iolo/a2ext/hw/a2ext-carrier/a2ext-carrier.kicad_sch

## KiCad design hw/a2ext-carrier/a2ext-carrier.kicad_sch (2026-09-17)

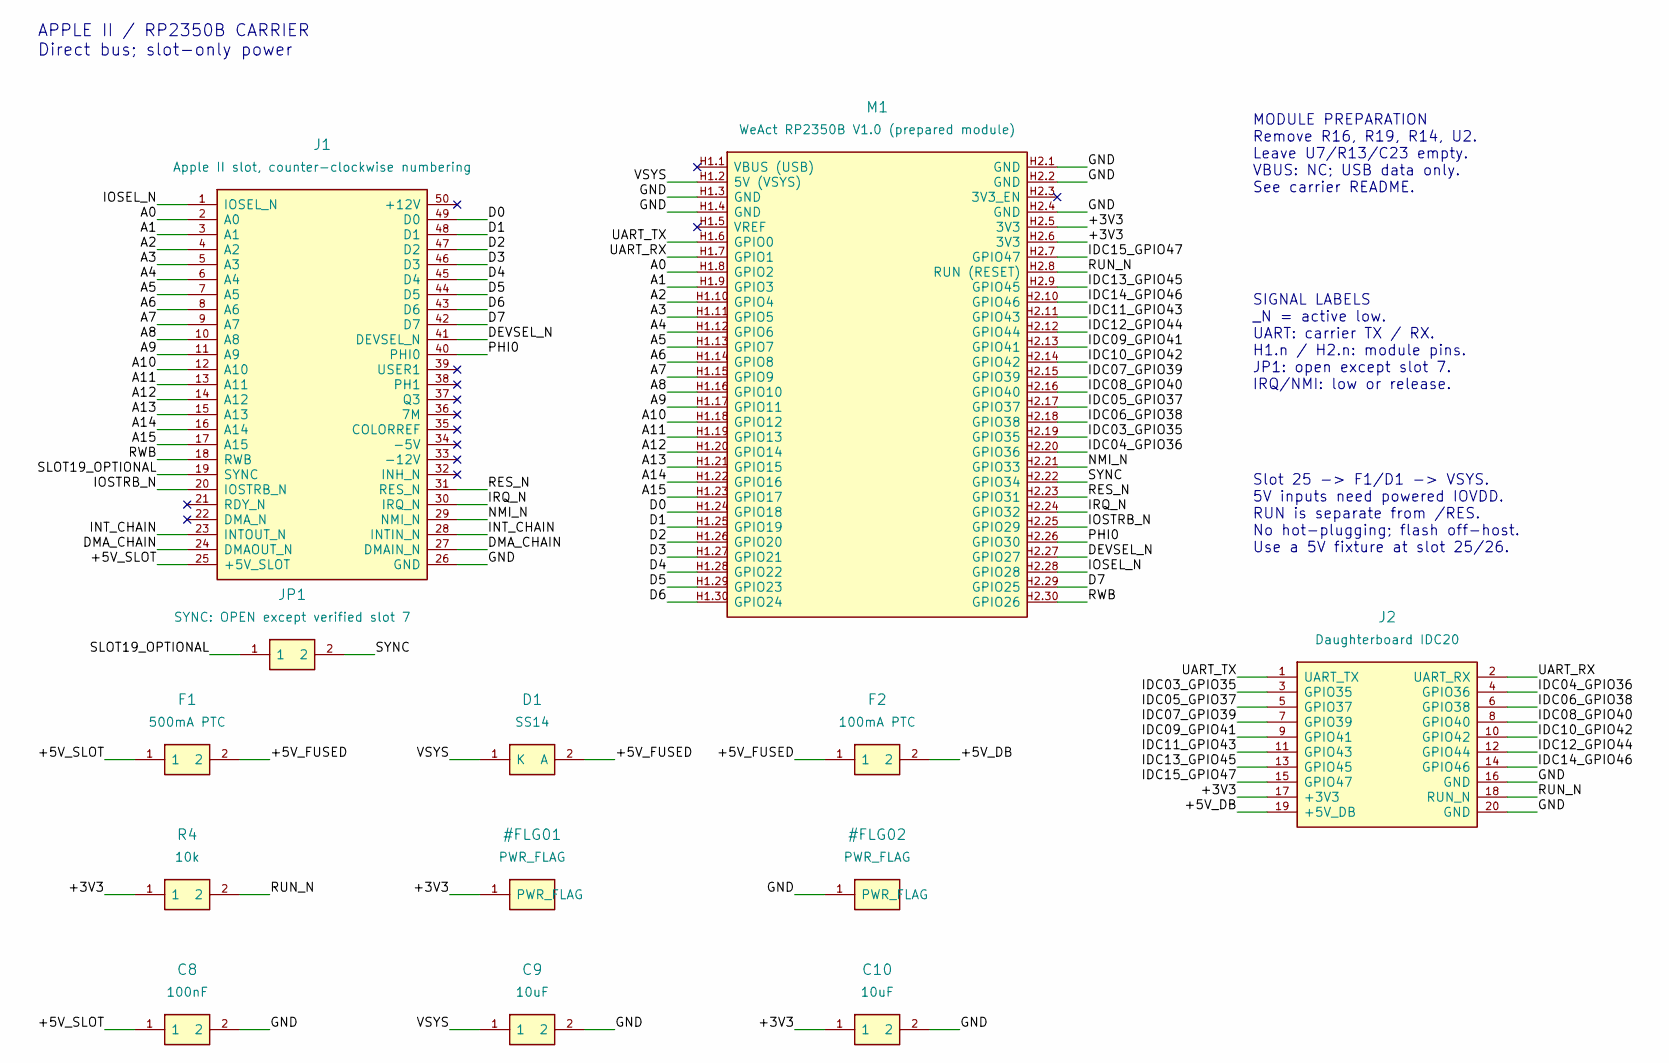
[picture p6: schematic a2ext-carrier.kicad_sch]

Parts:
C8: 100nF
C9, C10: 10uF
D1: SS14
F1: 500mA PTC
F2: 100mA PTC
J1: Apple II slot, counter-clockwise numbering
J2: Daughterboard IDC20
JP1: SYNC: OPEN except verified slot 7
M1: WeAct RP2350B V1.0 (prepared module)
R4: 10k

Connections:
+3V3: C10.1, J2.17 (+3V3), M1.H2.5 (3V3), M1.H2.6 (3V3), R4.1
+5V_DB: F2.2, J2.19 (+5V_DB)
+5V_FUSED: D1.2 (A), F1.2, F2.1
+5V_SLOT: C8.1, F1.1, J1.25 (+5V_SLOT)
A0: J1.2 (A0), M1.H1.8 (GPIO2)
A1: J1.3 (A1), M1.H1.9 (GPIO3)
A2: J1.4 (A2), M1.H1.10 (GPIO4)
A3: J1.5 (A3), M1.H1.11 (GPIO5)
A4: J1.6 (A4), M1.H1.12 (GPIO6)
A5: J1.7 (A5), M1.H1.13 (GPIO7)
A6: J1.8 (A6), M1.H1.14 (GPIO8)
A7: J1.9 (A7), M1.H1.15 (GPIO9)
A8: J1.10 (A8), M1.H1.16 (GPIO10)
A9: J1.11 (A9), M1.H1.17 (GPIO11)
A10: J1.12 (A10), M1.H1.18 (GPIO12)
A11: J1.13 (A11), M1.H1.19 (GPIO13)
A12: J1.14 (A12), M1.H1.20 (GPIO14)
A13: J1.15 (A13), M1.H1.21 (GPIO15)
A14: J1.16 (A14), M1.H1.22 (GPIO16)
A15: J1.17 (A15), M1.H1.23 (GPIO17)
D0: J1.49 (D0), M1.H1.24 (GPIO18)
D1: J1.48 (D1), M1.H1.25 (GPIO19)
D2: J1.47 (D2), M1.H1.26 (GPIO20)
D3: J1.46 (D3), M1.H1.27 (GPIO21)
D4: J1.45 (D4), M1.H1.28 (GPIO22)
D5: J1.44 (D5), M1.H1.29 (GPIO23)
D6: J1.43 (D6), M1.H1.30 (GPIO24)
D7: J1.42 (D7), M1.H2.29 (GPIO25)
DEVSEL_N: J1.41 (DEVSEL_N), M1.H2.27 (GPIO27)
DMA_CHAIN: J1.24 (DMAOUT_N), J1.27 (DMAIN_N)
GND: C8.2, C9.2, C10.2, J1.26 (GND), J2.16 (GND), J2.20 (GND), M1.H1.3 (GND), M1.H1.4 (GND), M1.H2.1 (GND), M1.H2.2 (GND), M1.H2.4 (GND)
IDC03_GPIO35: J2.3 (GPIO35), M1.H2.19 (GPIO35)
IDC04_GPIO36: J2.4 (GPIO36), M1.H2.20 (GPIO36)
IDC05_GPIO37: J2.5 (GPIO37), M1.H2.17 (GPIO37)
IDC06_GPIO38: J2.6 (GPIO38), M1.H2.18 (GPIO38)
IDC07_GPIO39: J2.7 (GPIO39), M1.H2.15 (GPIO39)
IDC08_GPIO40: J2.8 (GPIO40), M1.H2.16 (GPIO40)
IDC09_GPIO41: J2.9 (GPIO41), M1.H2.13 (GPIO41)
IDC10_GPIO42: J2.10 (GPIO42), M1.H2.14 (GPIO42)
IDC11_GPIO43: J2.11 (GPIO43), M1.H2.11 (GPIO43)
IDC12_GPIO44: J2.12 (GPIO44), M1.H2.12 (GPIO44)
IDC13_GPIO45: J2.13 (GPIO45), M1.H2.9 (GPIO45)
IDC14_GPIO46: J2.14 (GPIO46), M1.H2.10 (GPIO46)
IDC15_GPIO47: J2.15 (GPIO47), M1.H2.7 (GPIO47)
INT_CHAIN: J1.23 (INTOUT_N), J1.28 (INTIN_N)
IOSEL_N: J1.1 (IOSEL_N), M1.H2.28 (GPIO28)
IOSTRB_N: J1.20 (IOSTRB_N), M1.H2.25 (GPIO29)
IRQ_N: J1.30 (IRQ_N), M1.H2.24 (GPIO32)
NMI_N: J1.29 (NMI_N), M1.H2.21 (GPIO33)
PHI0: J1.40 (PHI0), M1.H2.26 (GPIO30)
RES_N: J1.31 (RES_N), M1.H2.23 (GPIO31)
RUN_N: J2.18 (RUN_N), M1.H2.8 (RUN (RESET)), R4.2
RWB: J1.18 (RWB), M1.H2.30 (GPIO26)
SLOT19_OPTIONAL: J1.19 (SYNC), JP1.1
SYNC: JP1.2, M1.H2.22 (GPIO34)
UART_RX: J2.2 (UART_RX), M1.H1.7 (GPIO1)
UART_TX: J2.1 (UART_TX), M1.H1.6 (GPIO0)
VSYS: C9.1, D1.1 (K), M1.H1.2 (5V (VSYS))

Notes on the sheet:
APPLE II / RP2350B CARRIER Direct bus; slot-only power
MODULE PREPARATION Remove R16, R19, R14, U2. Leave U7/R13/C23 empty. VBUS: NC; USB data only. See carrier README.
SIGNAL LABELS _N = active low. UART: carrier TX / RX. H1.n / H2.n: module pins. JP1: open except slot 7. IRQ/NMI: low or release.
Slot 25 -> F1/D1 -> VSYS. 5V inputs need powered IOVDD. RUN is separate from /RES. No hot-plugging; flash off-host. Use a 5V fixture at slot 25/26.
