iolo/a2ext/hw/a2ext-dvi/a2ext-dvi.kicad_sch

## KiCad design hw/a2ext-dvi/a2ext-dvi.kicad_sch (2026-09-17)

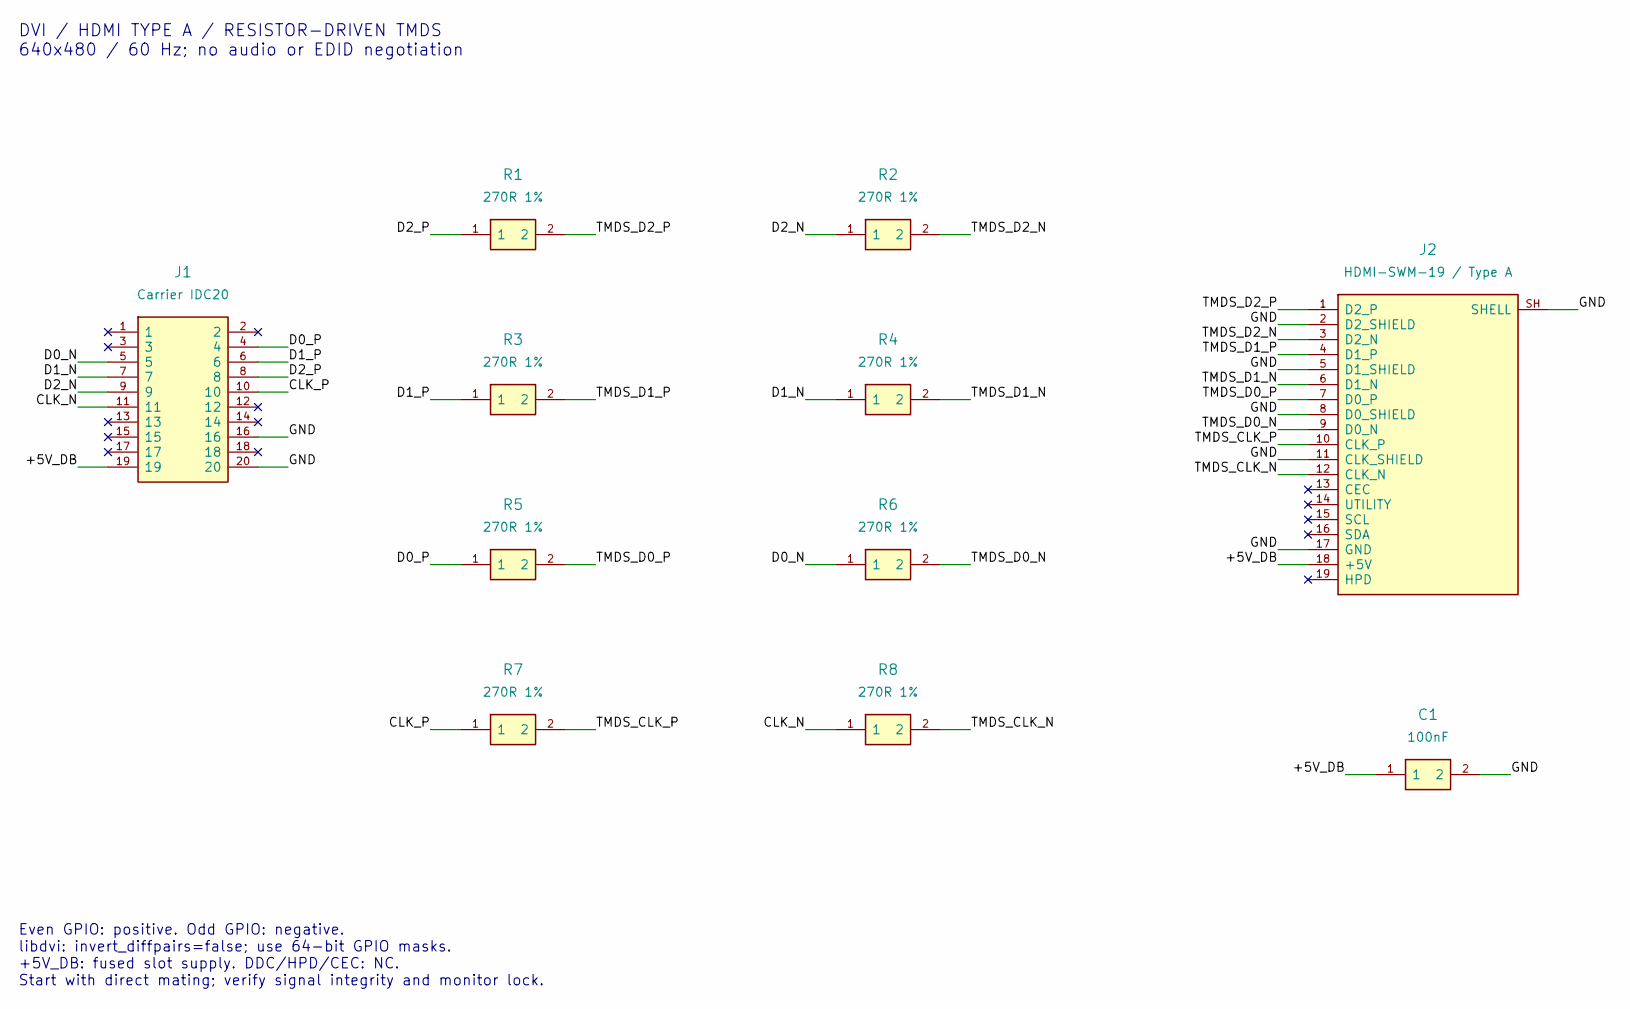
[picture p7: schematic a2ext-dvi.kicad_sch]

Parts:
C1: 100nF
J1: Carrier IDC20
J2: HDMI-SWM-19 / Type A
R1, R2, R3, R4, R5, R6, R7, R8: 270R 1%

Connections:
+5V_DB: C1.1, J1.19, J2.18 (+5V)
CLK_N: J1.11, R8.1
CLK_P: J1.10, R7.1
D0_N: J1.5, R6.1
D0_P: J1.4, R5.1
D1_N: J1.7, R4.1
D1_P: J1.6, R3.1
D2_N: J1.9, R2.1
D2_P: J1.8, R1.1
GND: C1.2, J1.16, J1.20, J2.2 (D2_SHIELD), J2.5 (D1_SHIELD), J2.8 (D0_SHIELD), J2.11 (CLK_SHIELD), J2.17 (GND), J2.SH (SHELL)
TMDS_CLK_N: J2.12 (CLK_N), R8.2
TMDS_CLK_P: J2.10 (CLK_P), R7.2
TMDS_D0_N: J2.9 (D0_N), R6.2
TMDS_D0_P: J2.7 (D0_P), R5.2
TMDS_D1_N: J2.6 (D1_N), R4.2
TMDS_D1_P: J2.4 (D1_P), R3.2
TMDS_D2_N: J2.3 (D2_N), R2.2
TMDS_D2_P: J2.1 (D2_P), R1.2

Notes on the sheet:
DVI / HDMI TYPE A / RESISTOR-DRIVEN TMDS 640x480 / 60 Hz; no audio or EDID negotiation
Even GPIO: positive. Odd GPIO: negative. libdvi: invert_diffpairs=false; use 64-bit GPIO masks. +5V_DB: fused slot supply. DDC/HPD/CEC: NC. Start with direct mating; verify signal integrity and monitor lock.
