iolo/a2ext/hw/a2ext-vga/a2ext-vga.kicad_sch

## KiCad design hw/a2ext-vga/a2ext-vga.kicad_sch (2026-09-17)

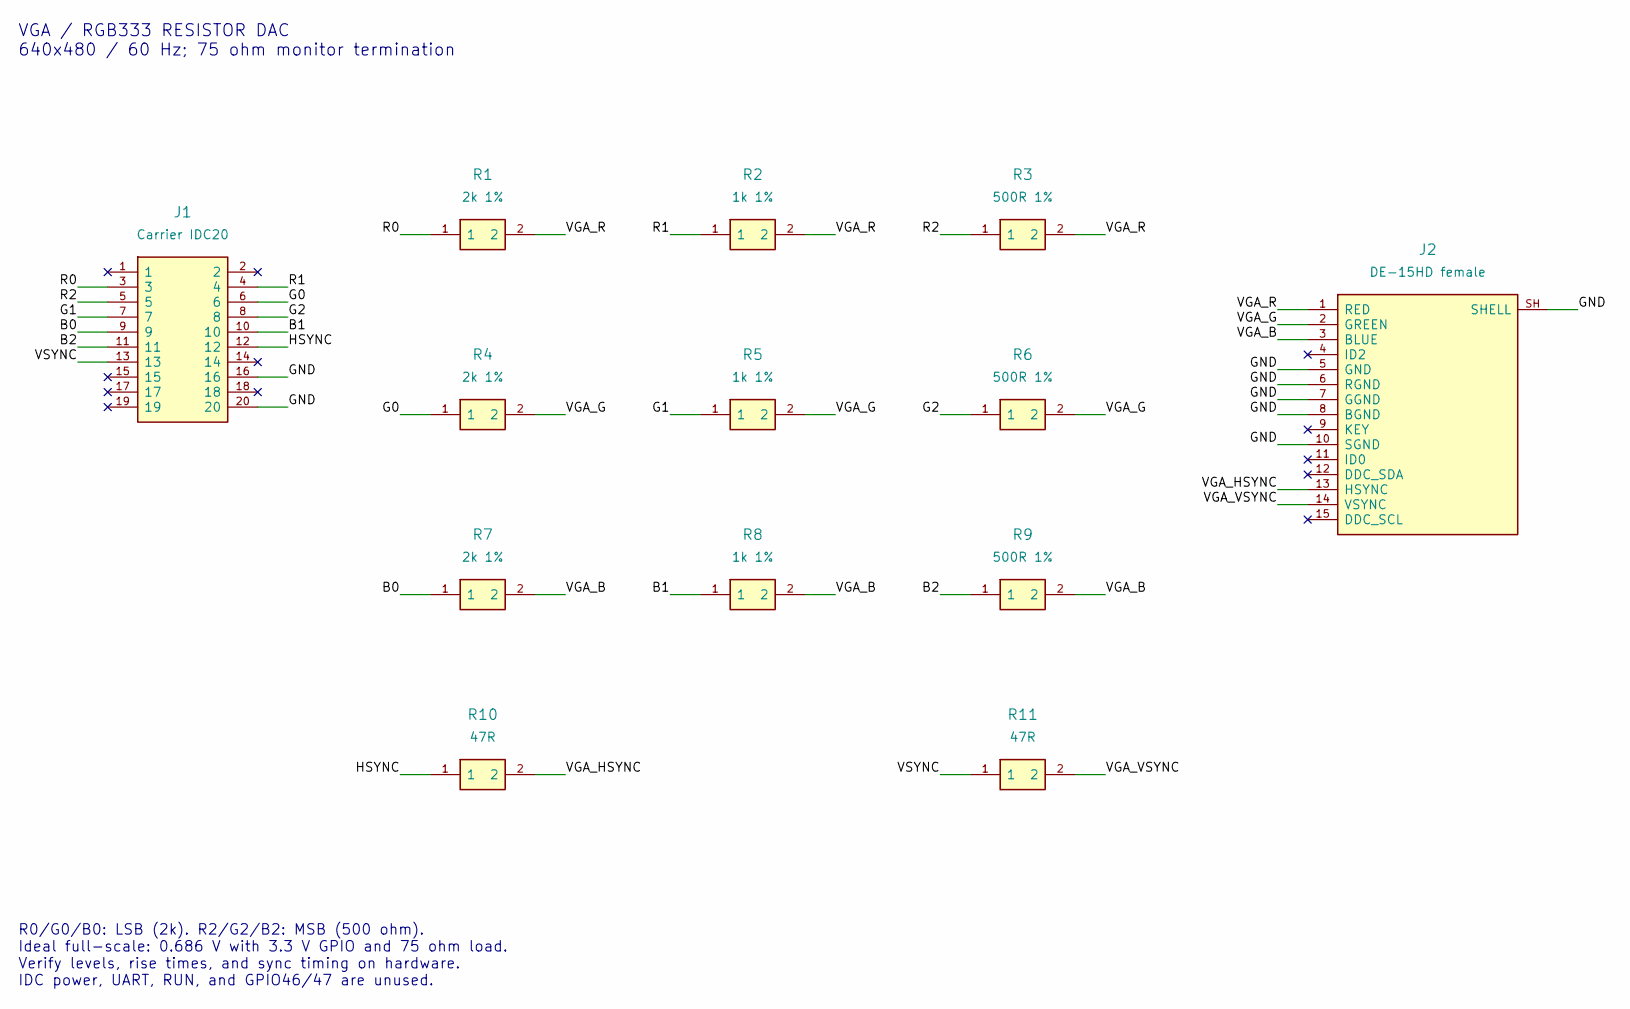
[picture p8: schematic a2ext-vga.kicad_sch]

Parts:
J1: Carrier IDC20
J2: DE-15HD female
R1, R4, R7: 2k 1%
R2, R5, R8: 1k 1%
R3, R6, R9: 500R 1%
R10, R11: 47R

Connections:
B0: J1.9, R7.1
B1: J1.10, R8.1
B2: J1.11, R9.1
G0: J1.6, R4.1
G1: J1.7, R5.1
G2: J1.8, R6.1
GND: J1.16, J1.20, J2.5 (GND), J2.6 (RGND), J2.7 (GGND), J2.8 (BGND), J2.10 (SGND), J2.SH (SHELL)
HSYNC: J1.12, R10.1
R0: J1.3, R1.1
R1: J1.4, R2.1
R2: J1.5, R3.1
VGA_B: J2.3 (BLUE), R7.2, R8.2, R9.2
VGA_G: J2.2 (GREEN), R4.2, R5.2, R6.2
VGA_HSYNC: J2.13 (HSYNC), R10.2
VGA_R: J2.1 (RED), R1.2, R2.2, R3.2
VGA_VSYNC: J2.14 (VSYNC), R11.2
VSYNC: J1.13, R11.1

Notes on the sheet:
VGA / RGB333 RESISTOR DAC 640x480 / 60 Hz; 75 ohm monitor termination
R0/G0/B0: LSB (2k). R2/G2/B2: MSB (500 ohm). Ideal full-scale: 0.686 V with 3.3 V GPIO and 75 ohm load. Verify levels, rise times, and sync timing on hardware. IDC power, UART, RUN, and GPIO46/47 are unused.
